cdrfiuba/programador/placa/placa_usb.sch

## KiCad design placa/placa_usb.sch (2015-01-24, an earlier design)

Schematic: placa_usb.sch

Parts:
C1, C5: 100n
C2: 100u
C3, C4: 22p
D1, D2: 3.6V
D3: LED_VERDE
D4: LED_ROJO
JP1: VCC
P5: USB_A
P6: ISP
P7: Targ.
R1, R2, R3, R4, R5: 1.5K
R6: 10K
R7, R8: 27
R9: 470k
U1: 74HC125N
U2: ATTINY2313DIP/SO
X1: 12MHz

Notes on the sheet:
GND
MOSI
VCC
RESET
SCK
MISO
de programacion
USB
de coneccion
interna
Conector
Programacion
LED Testigo
