cdrfiuba/programador/usbtinyisp/avr_spi.h

#ifndef _AVR_SPI_H_
#define _AVR_SPI_H_

#include "common.h"
#include "messages.h"
#include "macros.h"

byte_t	AVR_usb_in ( byte_t* data, byte_t len );
void	AVR_usb_out ( byte_t* data, byte_t len );
byte_t  AVR_usb_setup(byte_t data[8]);

#endif
